kikeelectronico/boton-telegram/photos/photo_1.jpg

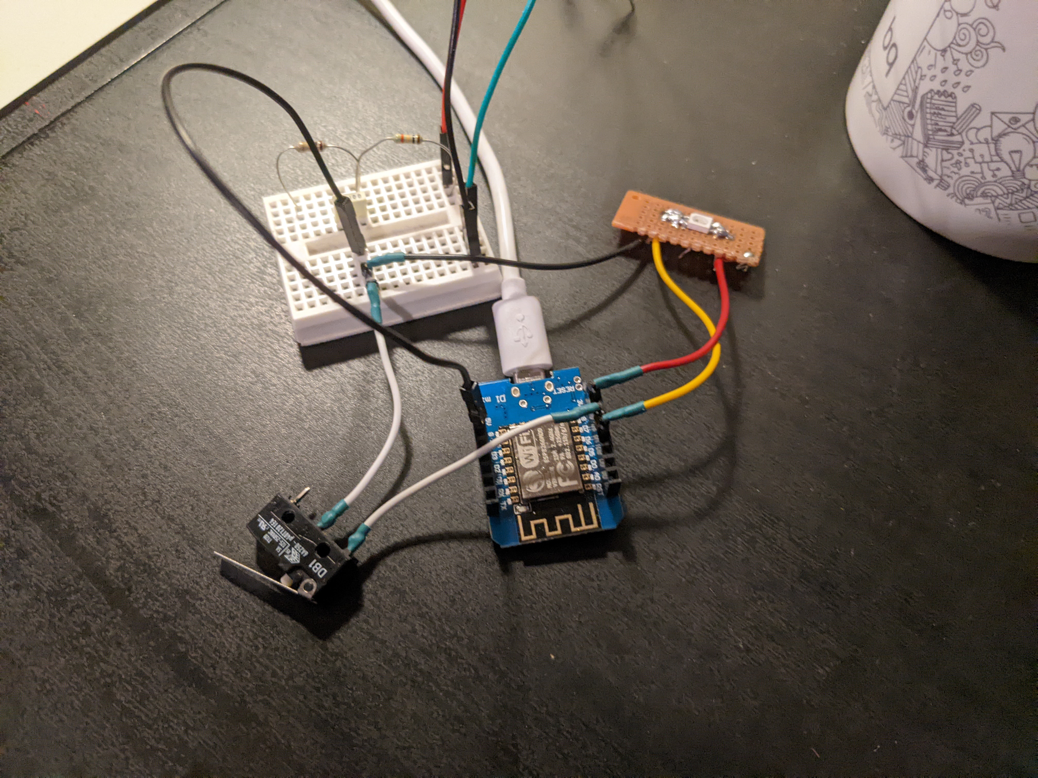
photos/photo_1.jpg
