kikeelectronico/boton-telegram/photos/photo_2.jpg

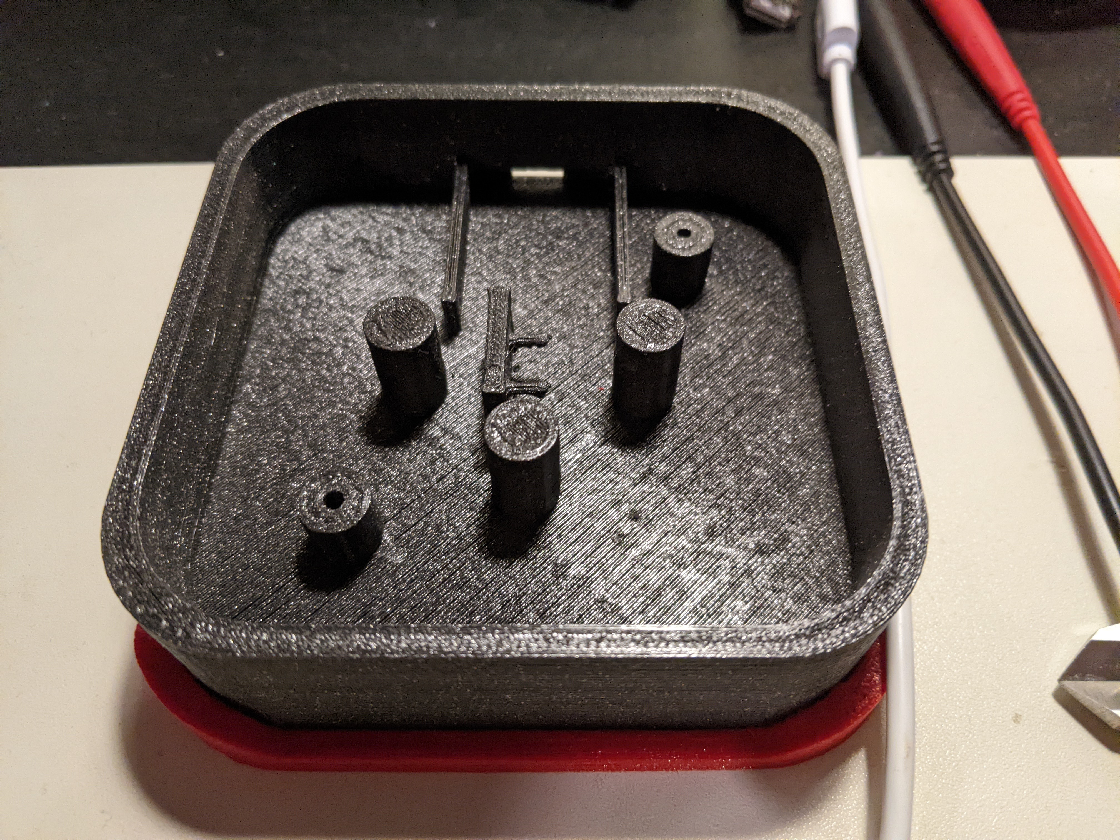
photos/photo_2.jpg
