kikeelectronico/boton-telegram/photos/photo_3.jpg

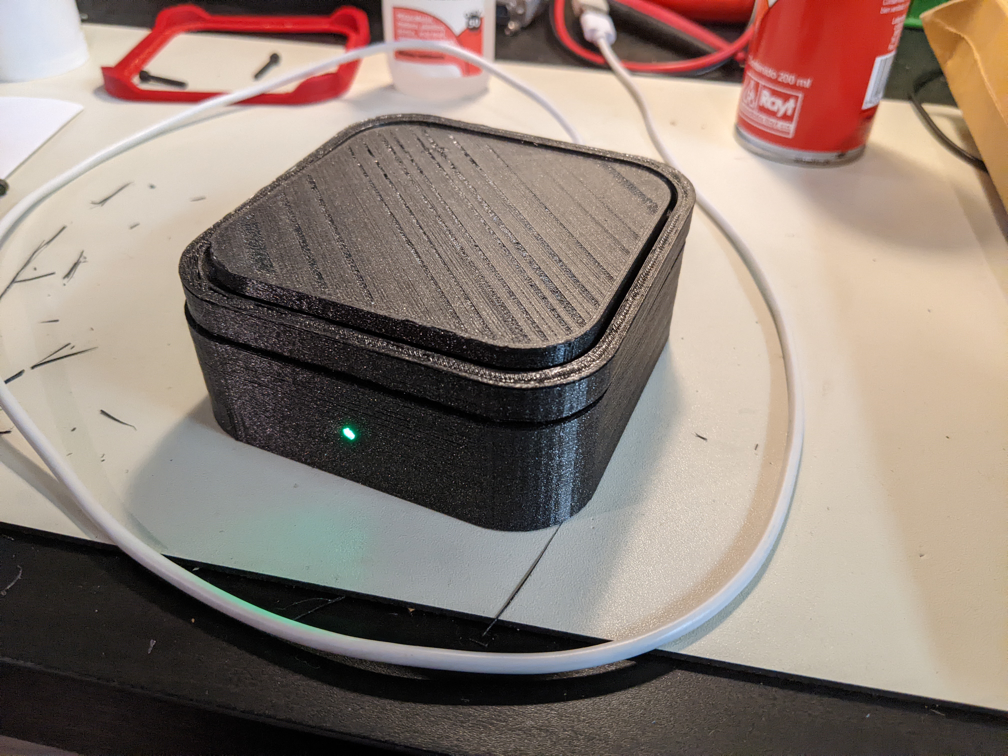
photos/photo_3.jpg
