kikeelectronico/boton-telegram/photos/photo_5.jpg

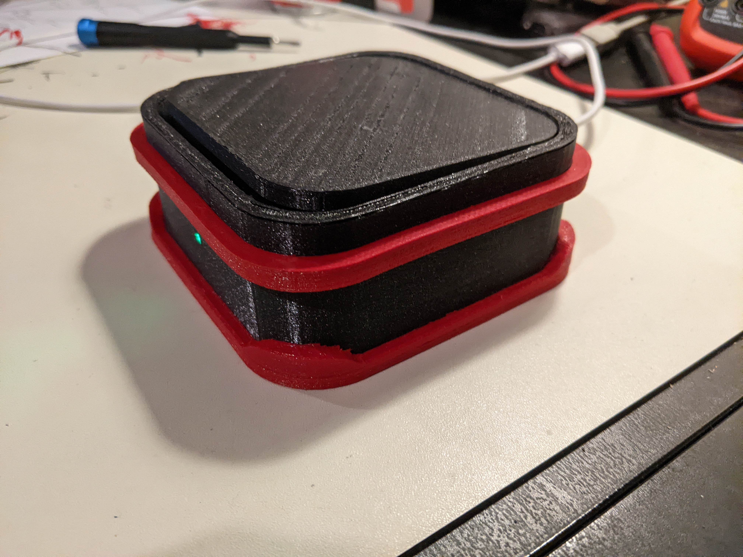
photos/photo_5.jpg
