kikeelectronico/boton-telegram/photos/photo_6.jpg

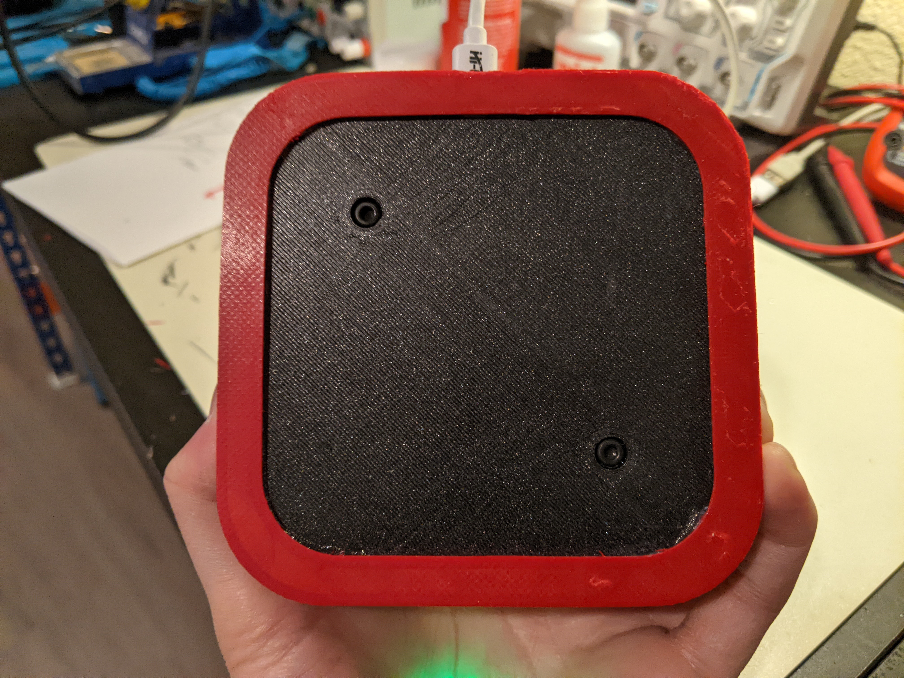
photos/photo_6.jpg
