kikeelectronico/boton-telegram/photos/photo_7.jpg

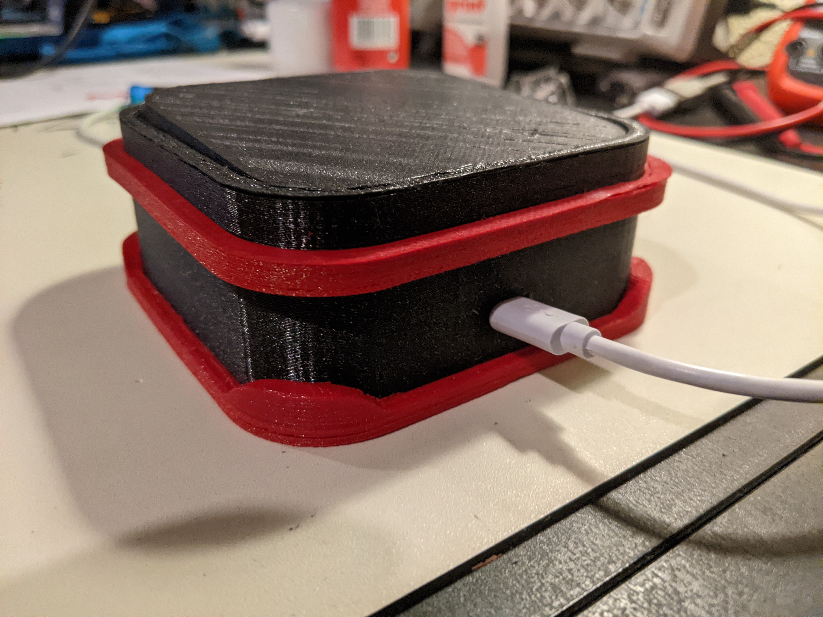
photos/photo_7.jpg
